myriadrf/LimeSDR-XTRX/hardware/rev5/Project Outputs/Pics/8L single outer 50.png

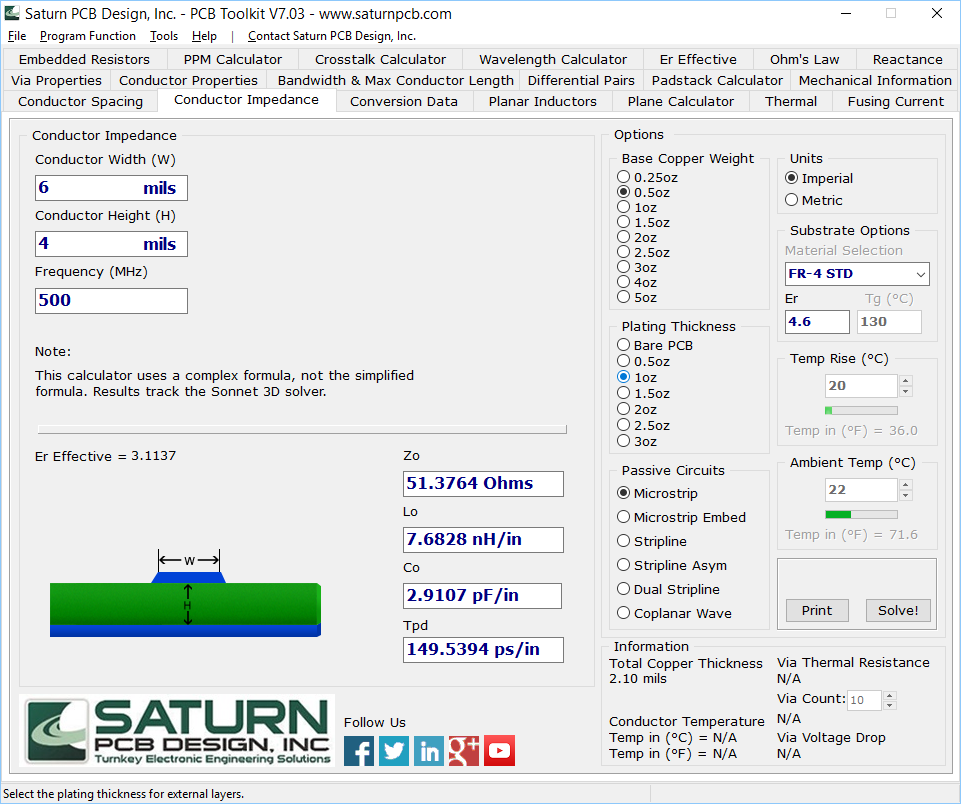
hardware/rev5/Project Outputs/Pics/8L single outer 50.png
