myriadrf/LimeSDR-XTRX/hardware/rev5/Project Outputs/Pics/8L stack.png

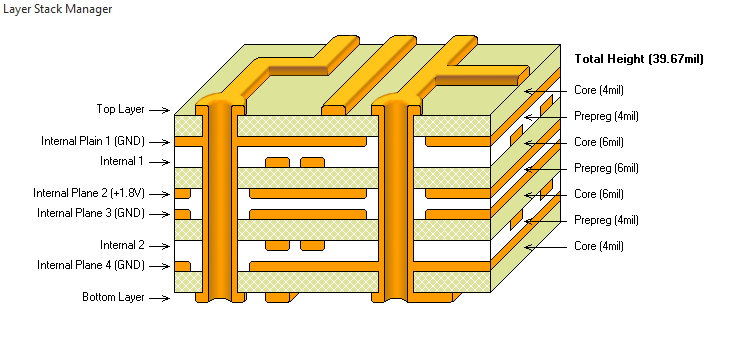
hardware/rev5/Project Outputs/Pics/8L stack.png
