myriadrf/LimeSDR-XTRX/hardware/rev5/Project Outputs/Pics/ARTIX-XC7A35T.jpg

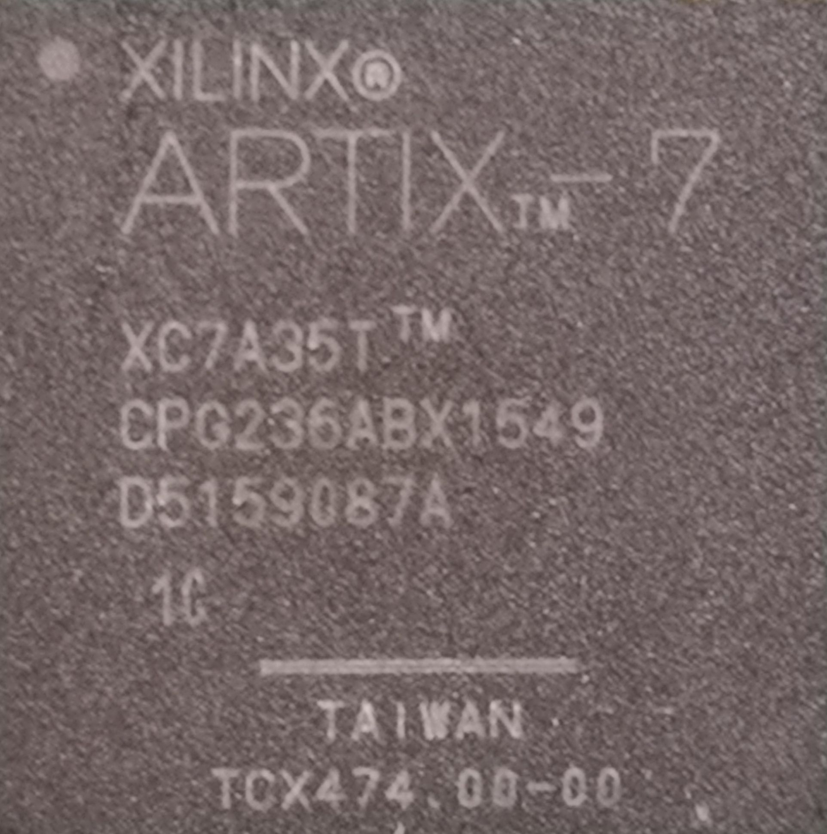
hardware/rev5/Project Outputs/Pics/ARTIX-XC7A35T.jpg
