myriadrf/LimeSDR-XTRX/hardware/rev5/Project Outputs/Pics/FPC Connector.png

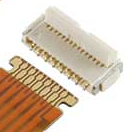
hardware/rev5/Project Outputs/Pics/FPC Connector.png
