myriadrf/LimeSDR-XTRX/hardware/rev5/Project Outputs/Pics/GPIO.jpg

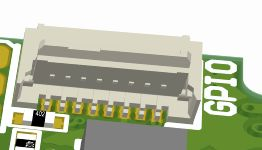
hardware/rev5/Project Outputs/Pics/GPIO.jpg
