myriadrf/LimeSDR-XTRX/hardware/rev5/Project Outputs/Pics/GPS Module.jpg

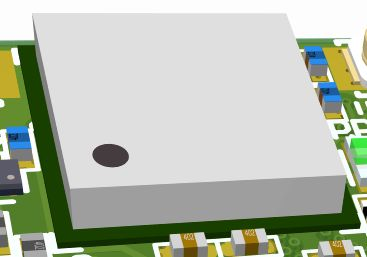
hardware/rev5/Project Outputs/Pics/GPS Module.jpg
