myriadrf/LimeSDR-XTRX/hardware/rev5/Project Outputs/Pics/JTAG.jpg

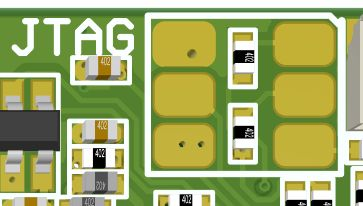
hardware/rev5/Project Outputs/Pics/JTAG.jpg
