myriadrf/LimeSDR-XTRX/hardware/rev5/Project Outputs/Pics/LMS7002M.jpg

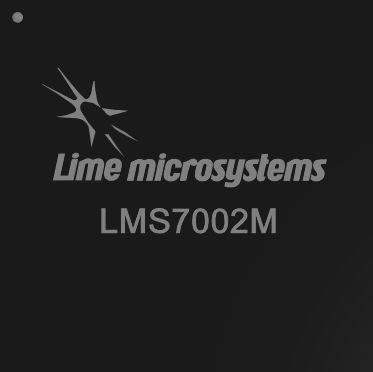
hardware/rev5/Project Outputs/Pics/LMS7002M.jpg
