myriadrf/LimeSDR-XTRX/hardware/rev5/Project Outputs/Pics/microUSB connector.jpg

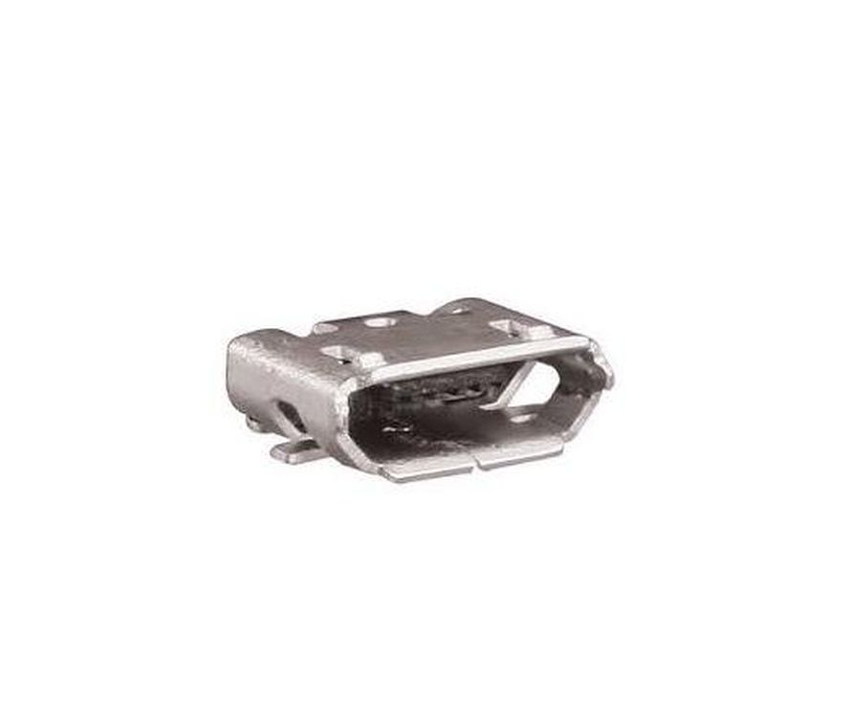
hardware/rev5/Project Outputs/Pics/microUSB connector.jpg
