myriadrf/LimeSDR-XTRX/hardware/rev5/Project Outputs/Pics/miniPCIe edge connector.jpg

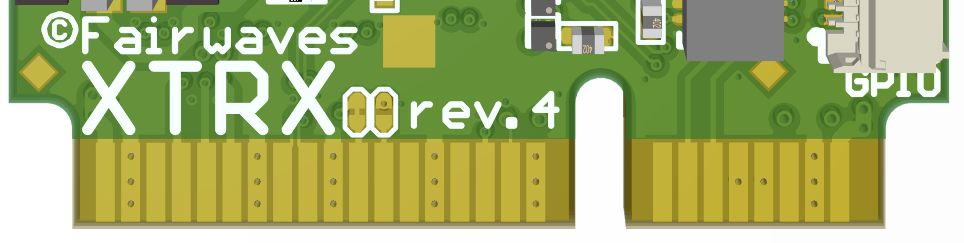
hardware/rev5/Project Outputs/Pics/miniPCIe edge connector.jpg
