myriadrf/LimeSDR-XTRX/hardware/rev5/Project Outputs/Pics/Rx IQ Input.jpg

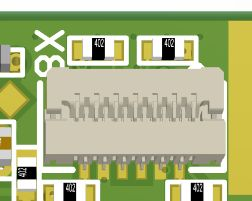
hardware/rev5/Project Outputs/Pics/Rx IQ Input.jpg
