myriadrf/LimeSDR-XTRX/hardware/rev5/Project Outputs/Pics/Transparently.png

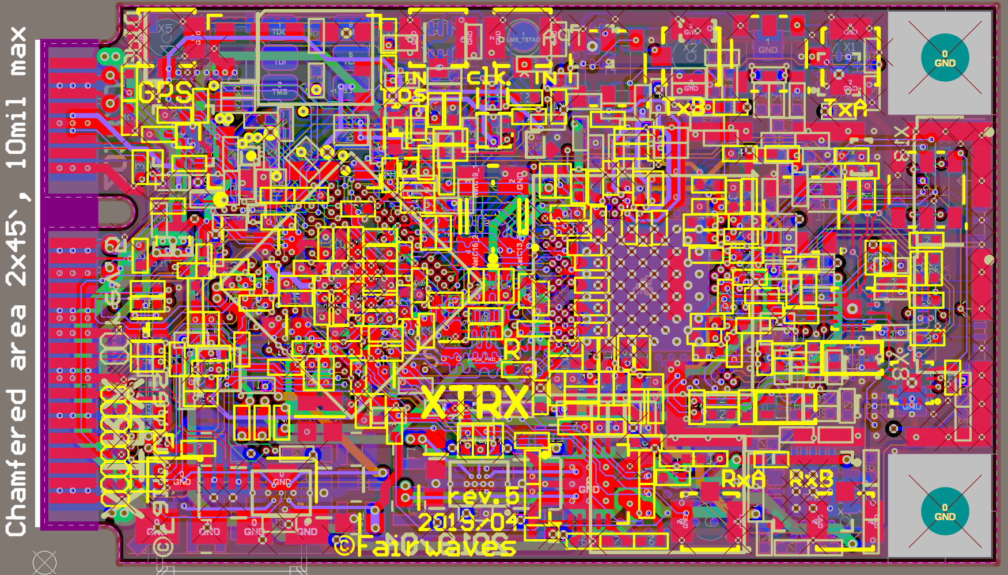
hardware/rev5/Project Outputs/Pics/Transparently.png
