myriadrf/LimeSDR-XTRX/hardware/rev5/Project Outputs/Pics/XTRXr5 pcb stack example.png

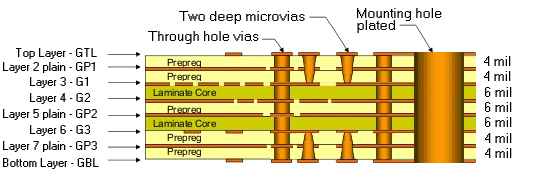
hardware/rev5/Project Outputs/Pics/XTRXr5 pcb stack example.png
