myriadrf/LimeSDR-XTRX/hardware/rev5/Project Outputs/XTRXr5 Func Diagram.PDF

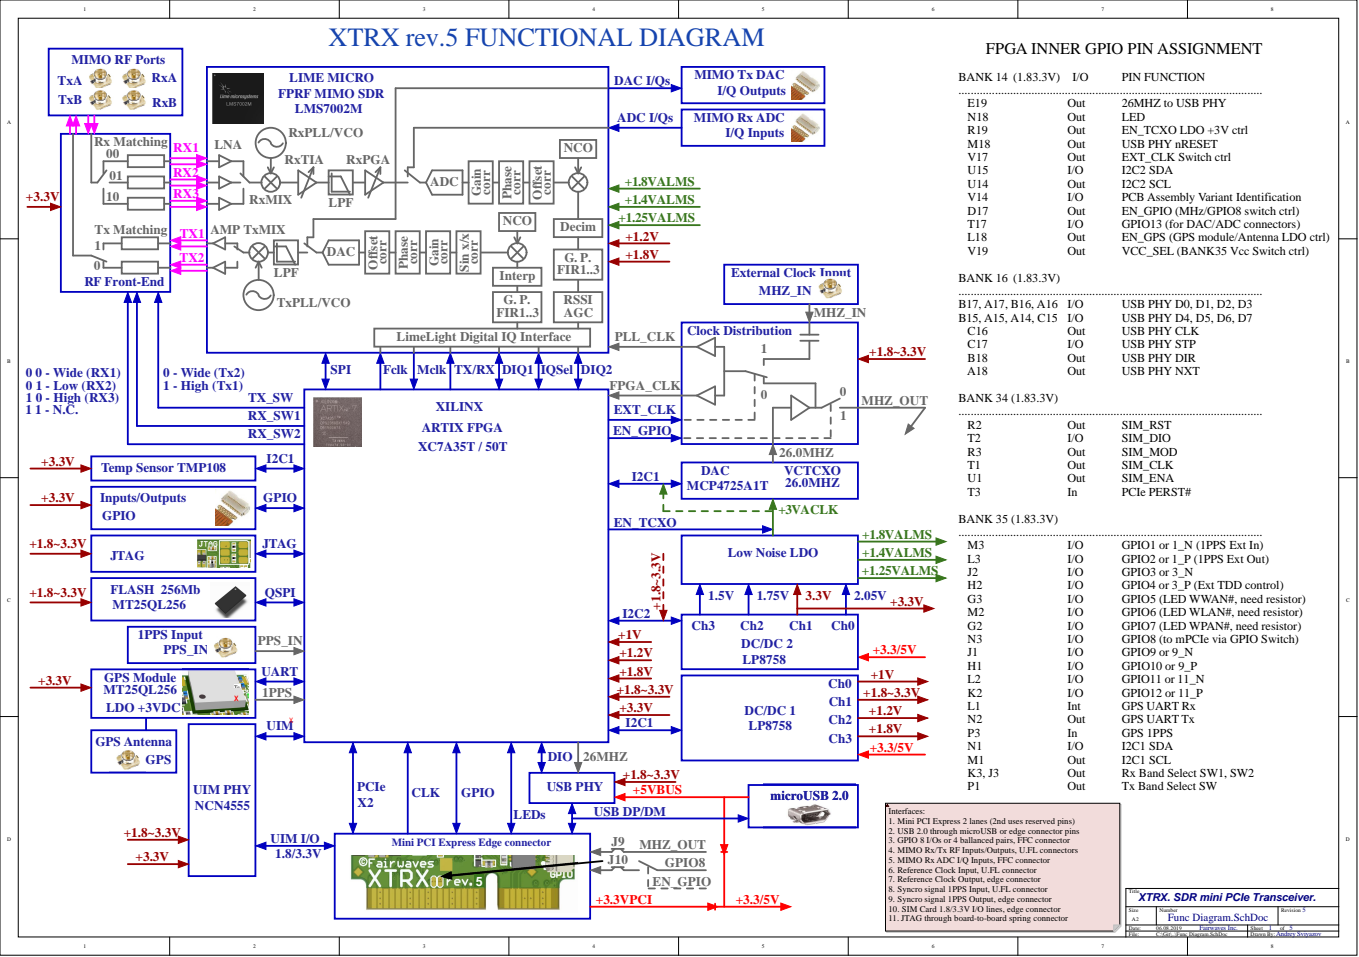
[picture p20: page 1]

XTRX rev.5 FUNCTIONAL DIAGRAM

FPGA INNER GPIO PIN ASSIGNMENT

LimeLight Digital IQ Interface

Interfaces:
1. Mini PCI Express 2 lanes (2nd uses reserved pins)
2. USB 2.0 through microUSB or edge connector pins
3. GPIO 8 I/Os or 4 ballanced pairs, FFC connector
4. MIMO Rx/Tx RF Inputs/Outputs, U.FL connectors
5. MIMO Rx ADC I/Q Inputs, FFC connector
6. Reference Clock Input, U.FL connector
7. Reference Clock Output, edge connector
8. Syncro signal 1PPS Input, U.FL connector
9. Syncro signal 1PPS Output, edge connector
10. SIM Card 1.8/3.3V I/O lines, edge connector
11. JTAG through board-to-board spring connector

Mini PCI Express Edge connector

Title
XTRX. SDR mini PCIe Transceiver.
