myriadrf/LimeSDR-XTRX/hardware/rev5/Project Outputs/XTRXr5_SCH_(Var 3.3V_I).pdf

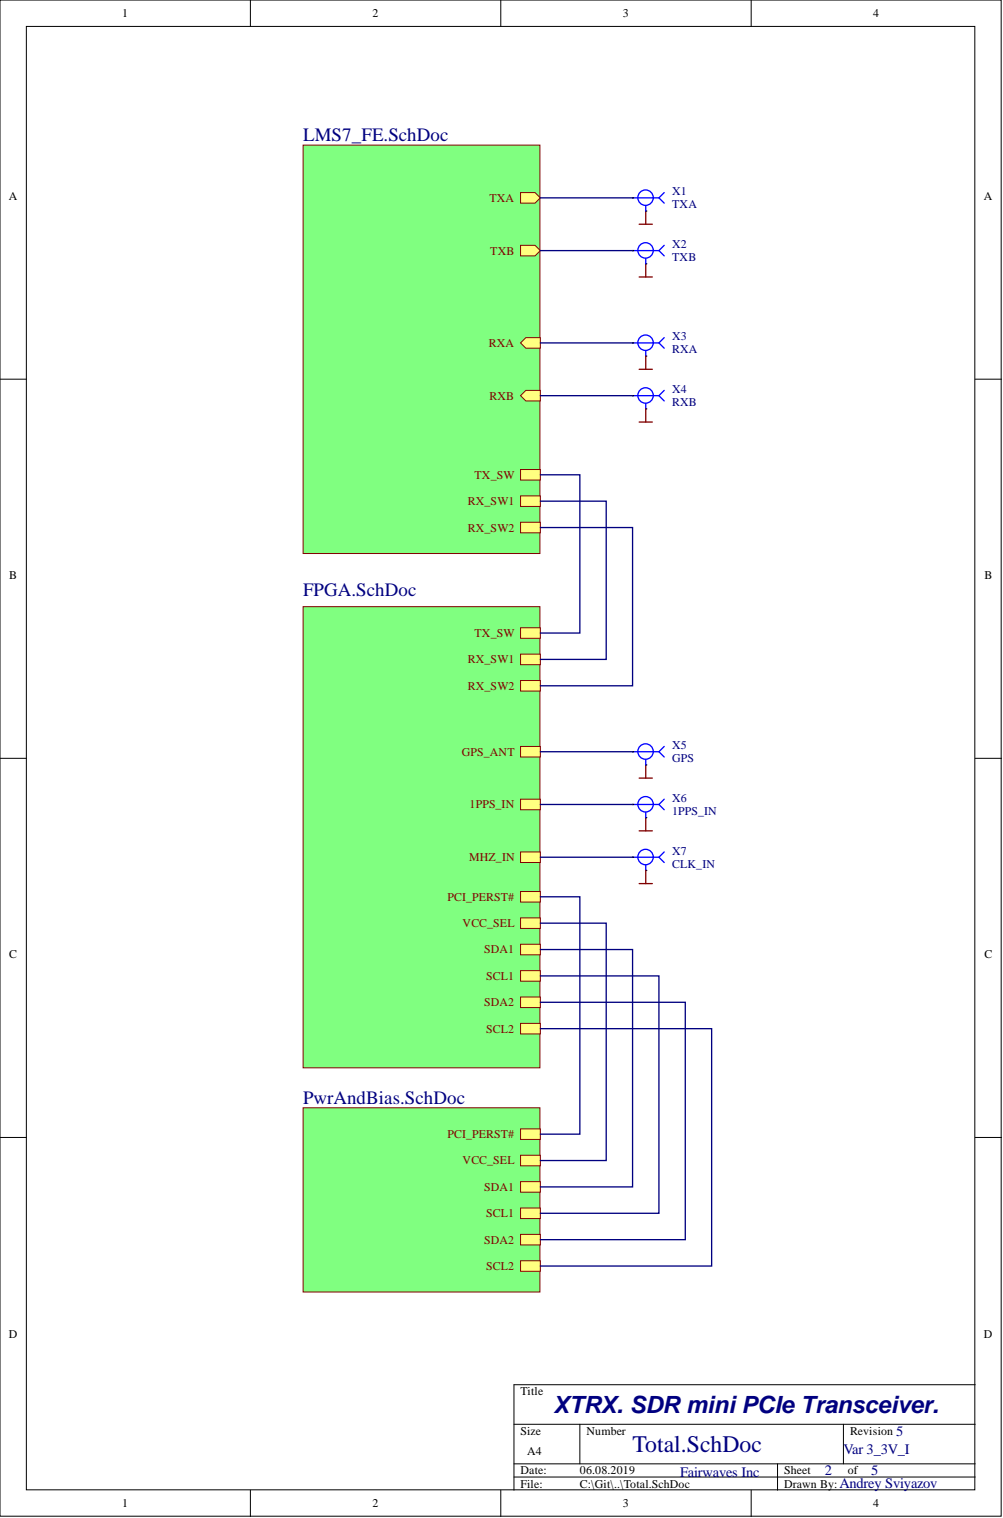
[picture p21: page 1]

Title
XTRX. SDR mini PCIe Transceiver.

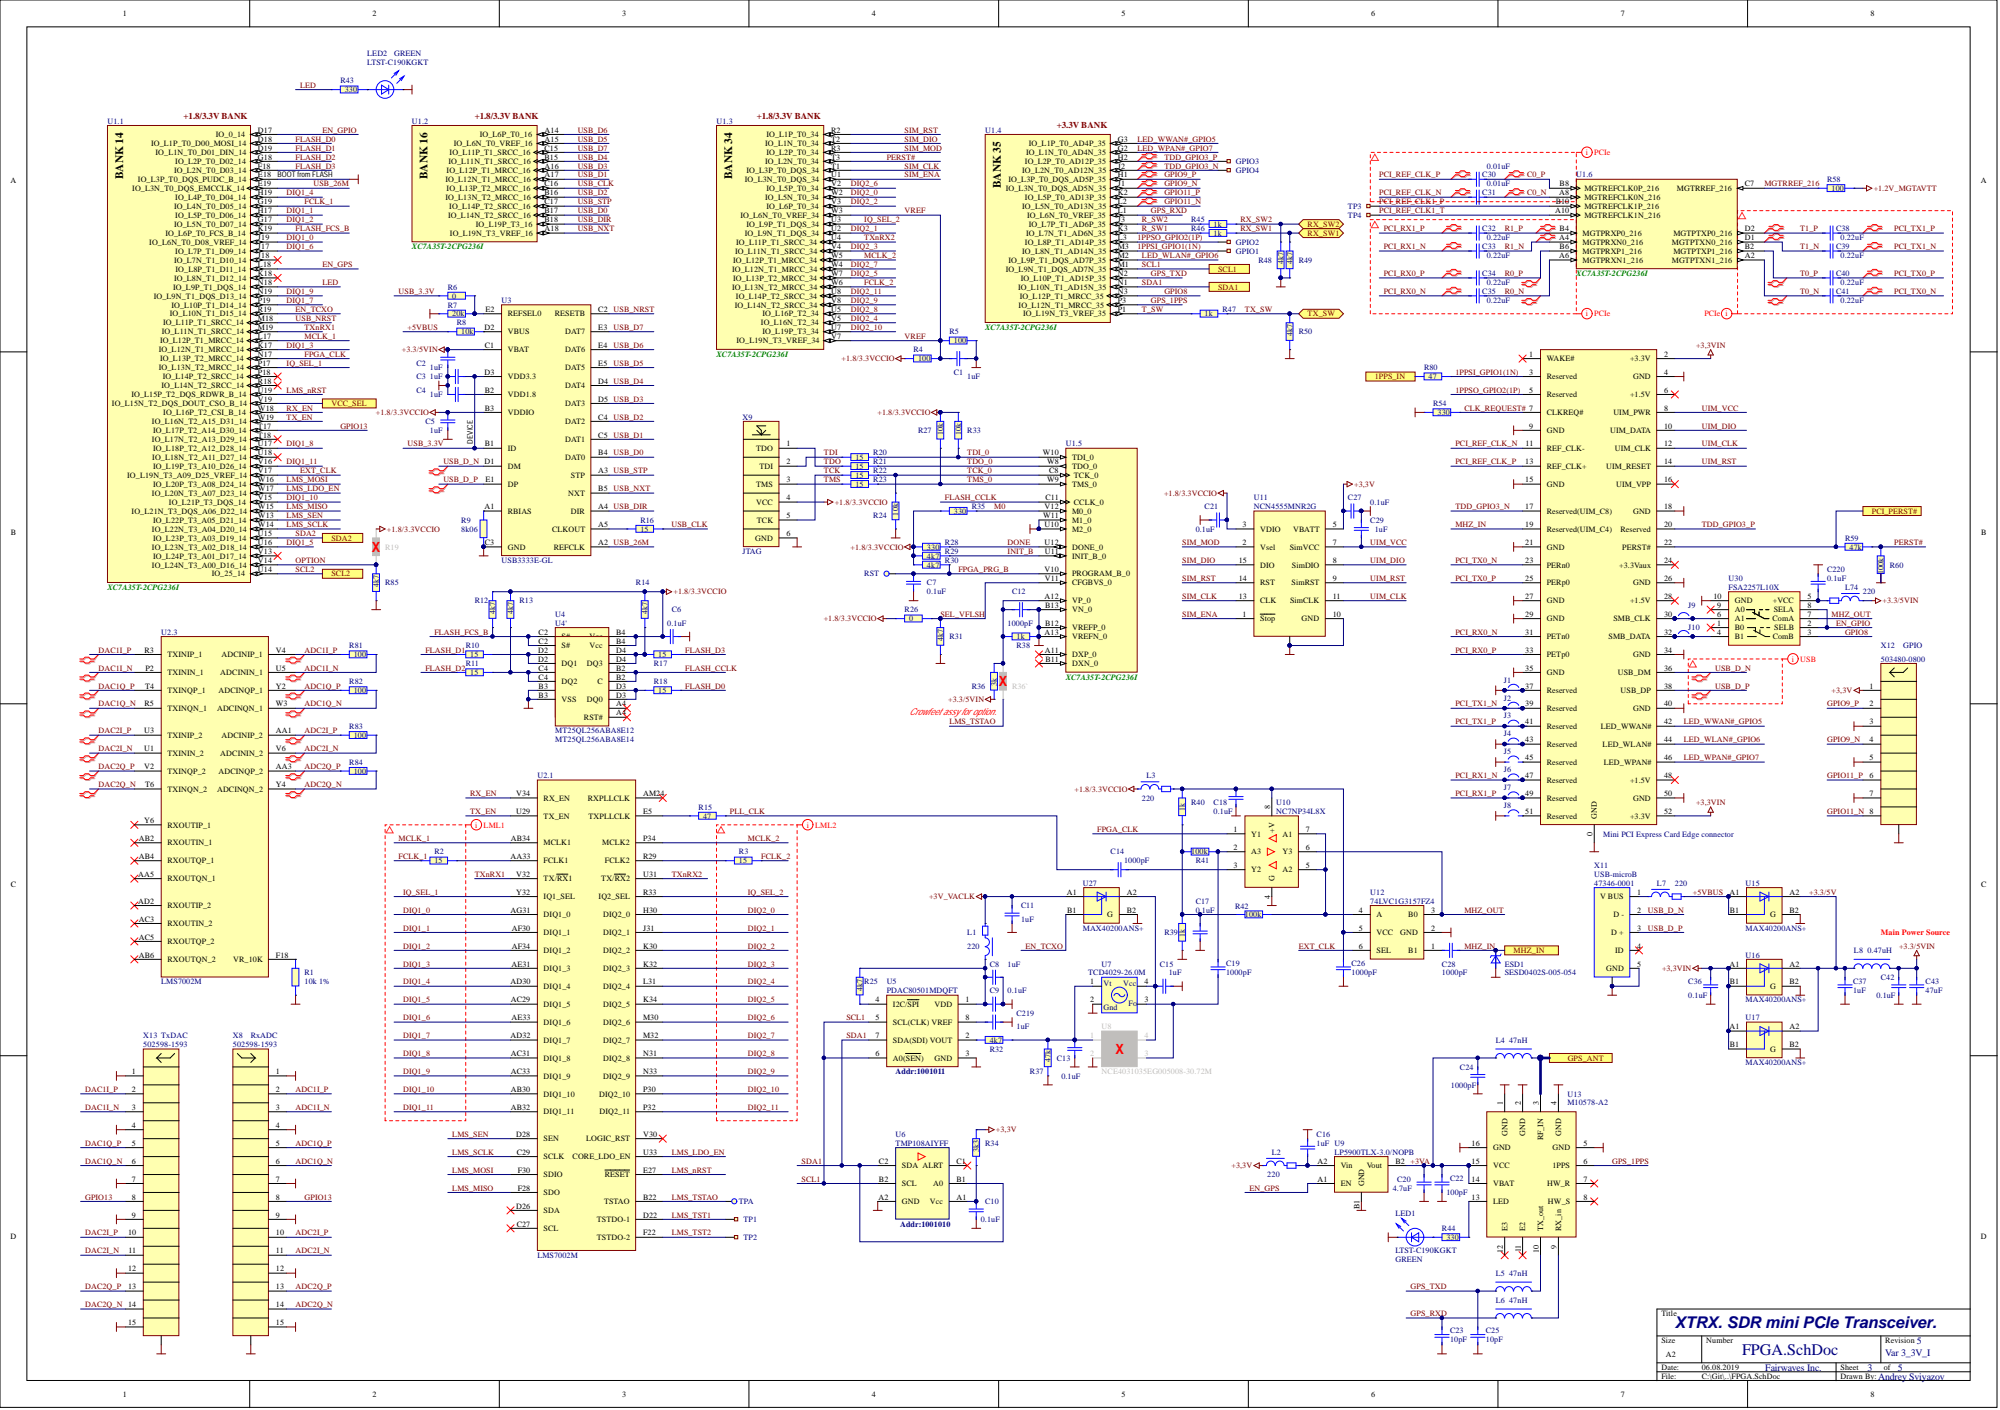
[picture p22: page 2]

Crowfeet assy for option.

ADC2Q_N | 100

Mini PCI Express Card Edge connector

SDA1 | SDA(SDI) 7

A0(SEN) 6

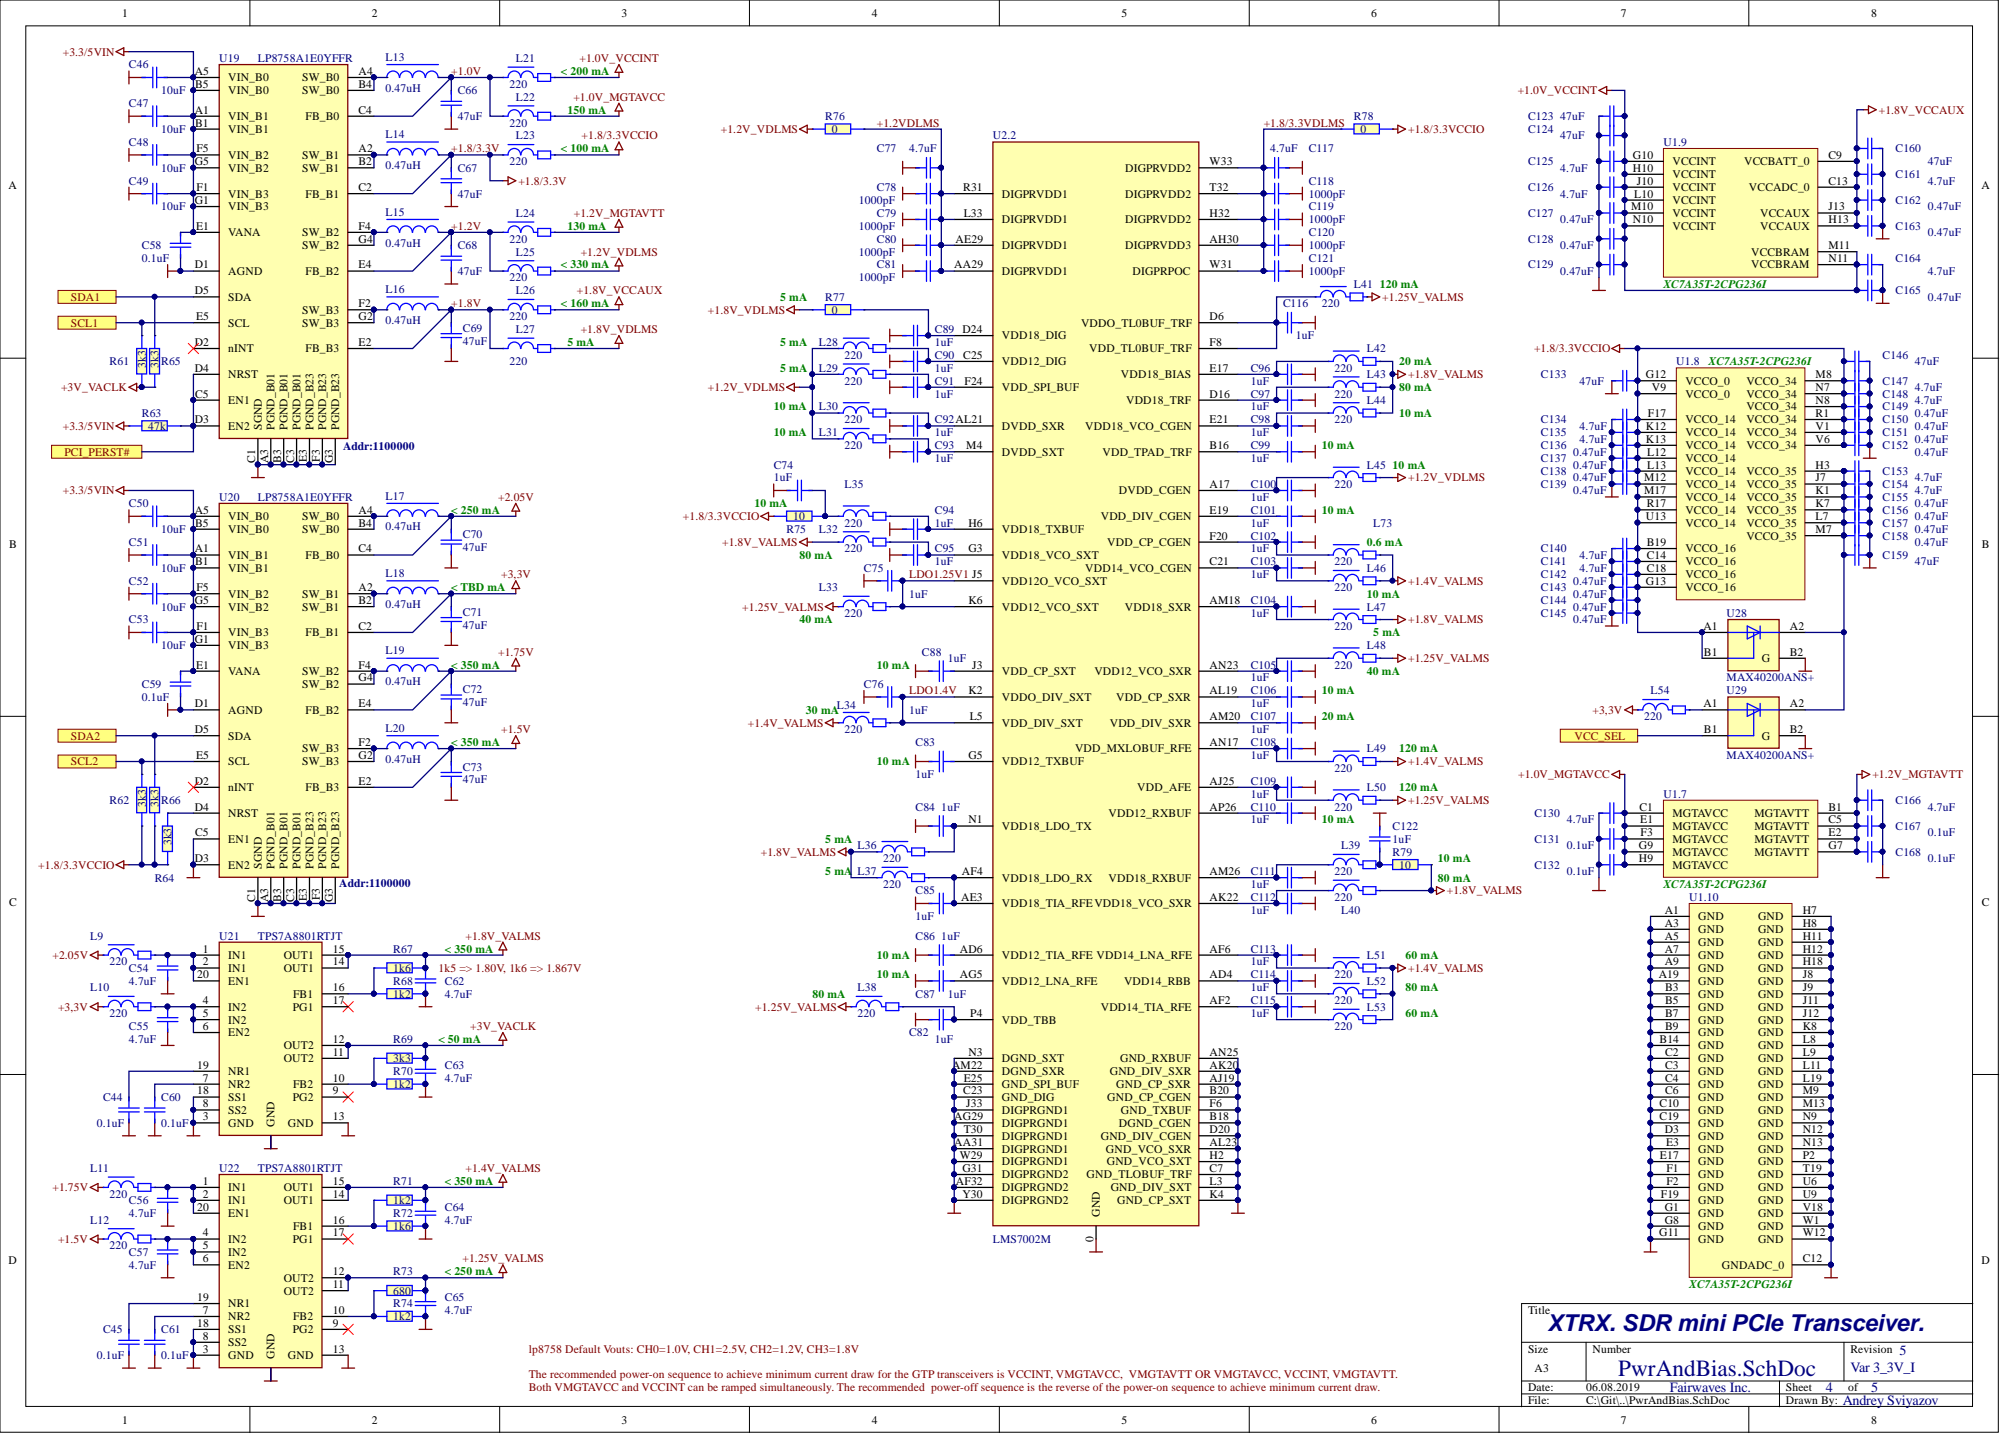
[picture p23: page 3]

J 7
K 1

A 3 | H 8
A 5 | H 1 1

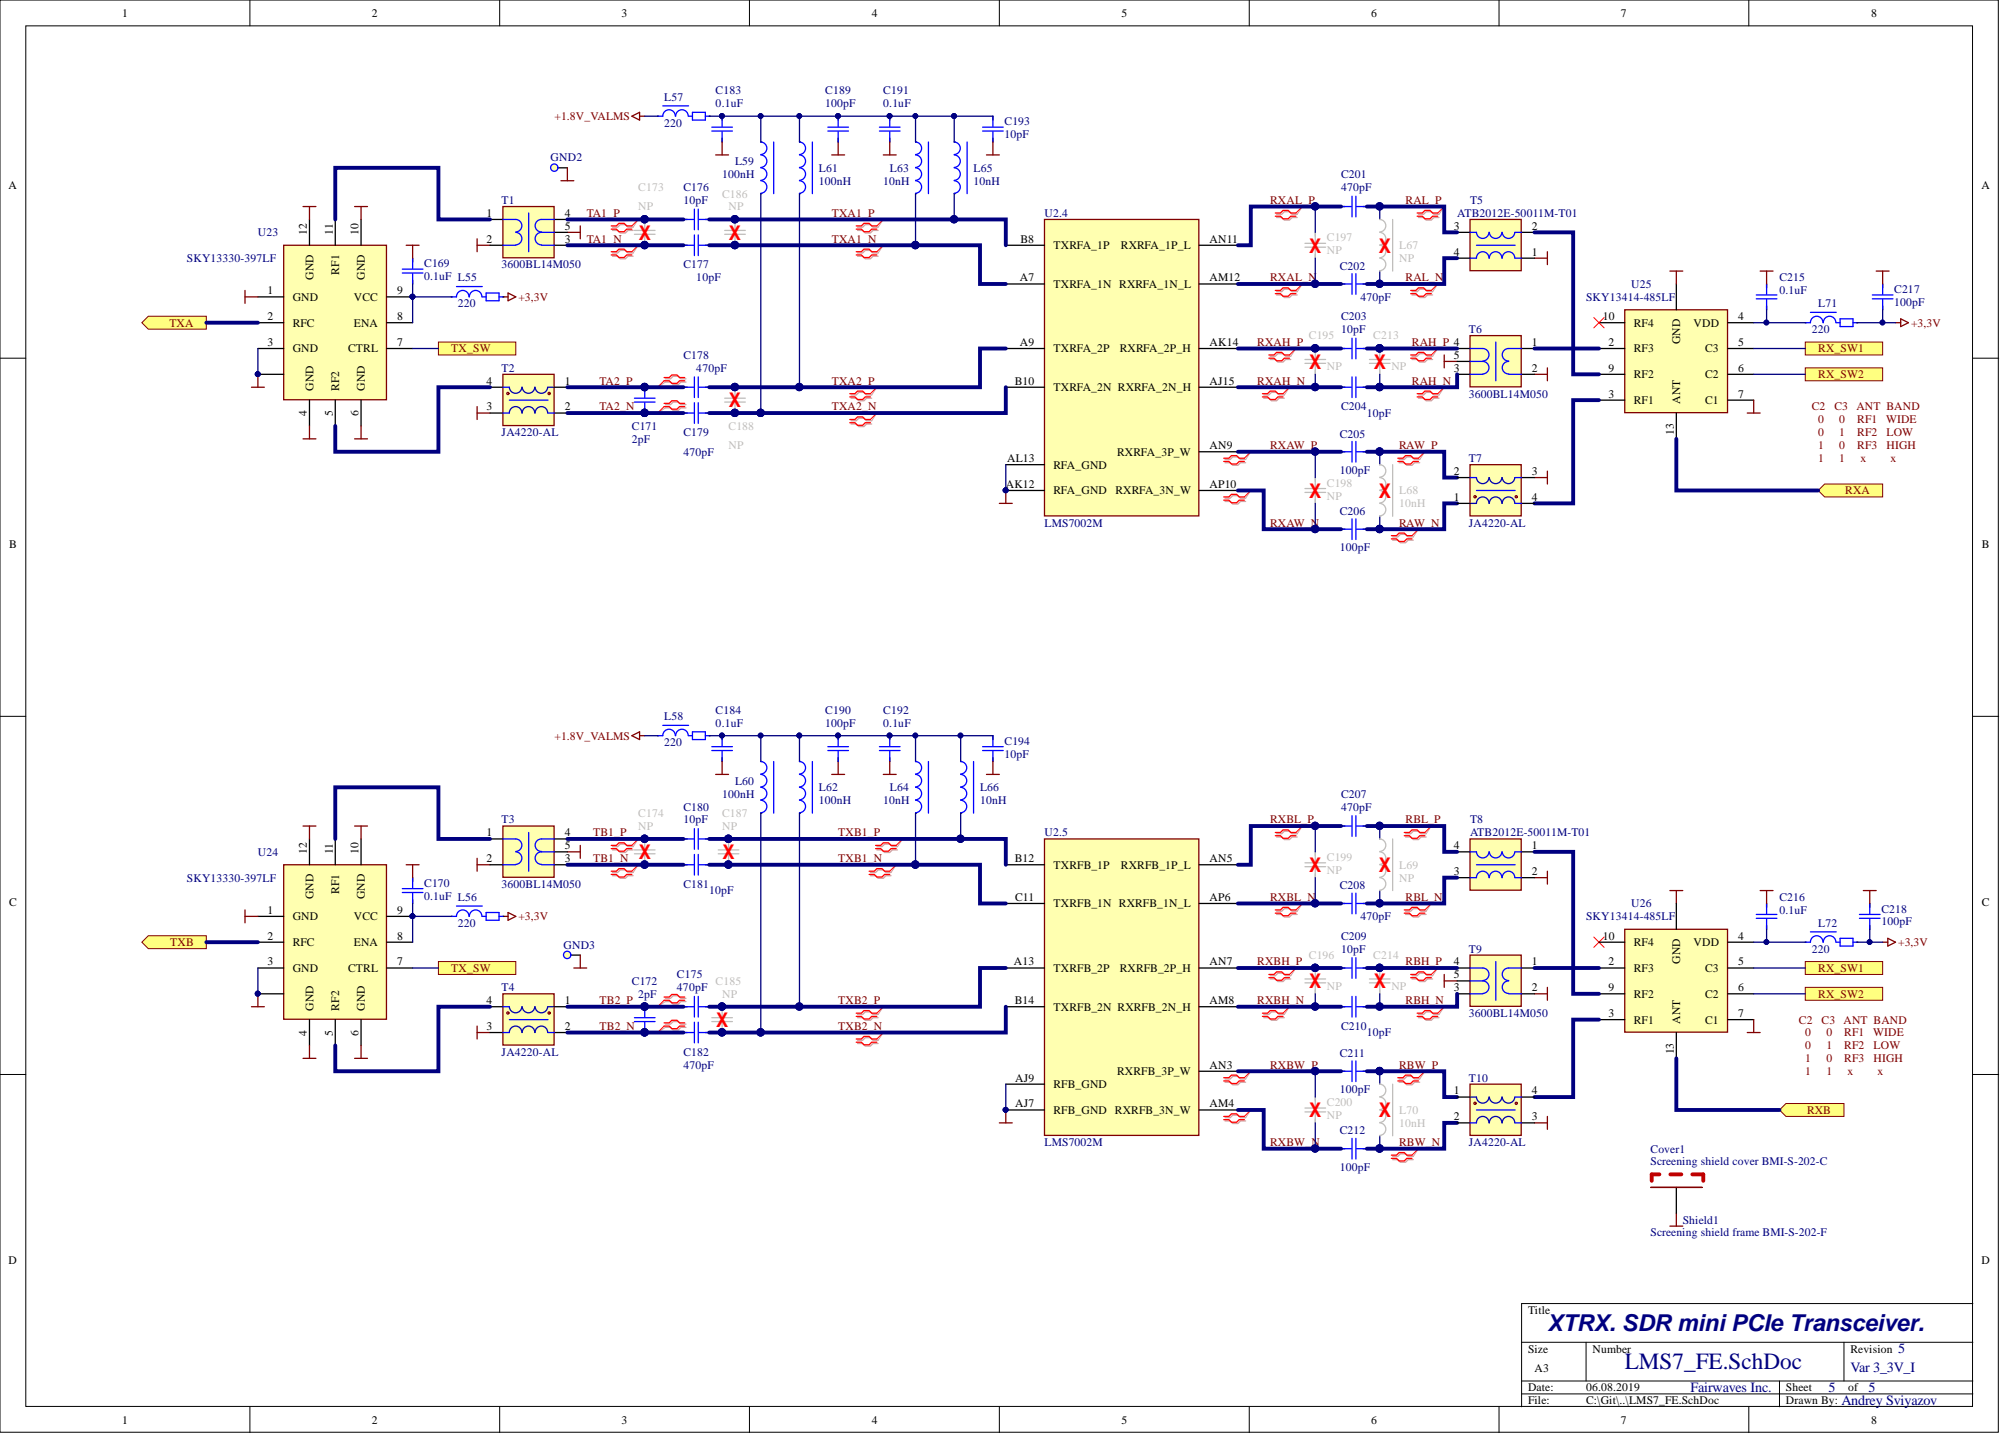
[picture p24: page 4]

RXAW_N

RAW_N

Cover1
Screening shield cover BMI-S-202-C

Shield1
Screening shield frame BMI-S-202-F
