myriadrf/LimeSDR-XTRX/hardware/rev5/Project Outputs/XTRXr5_assembly_(Var 3.3V).PDF

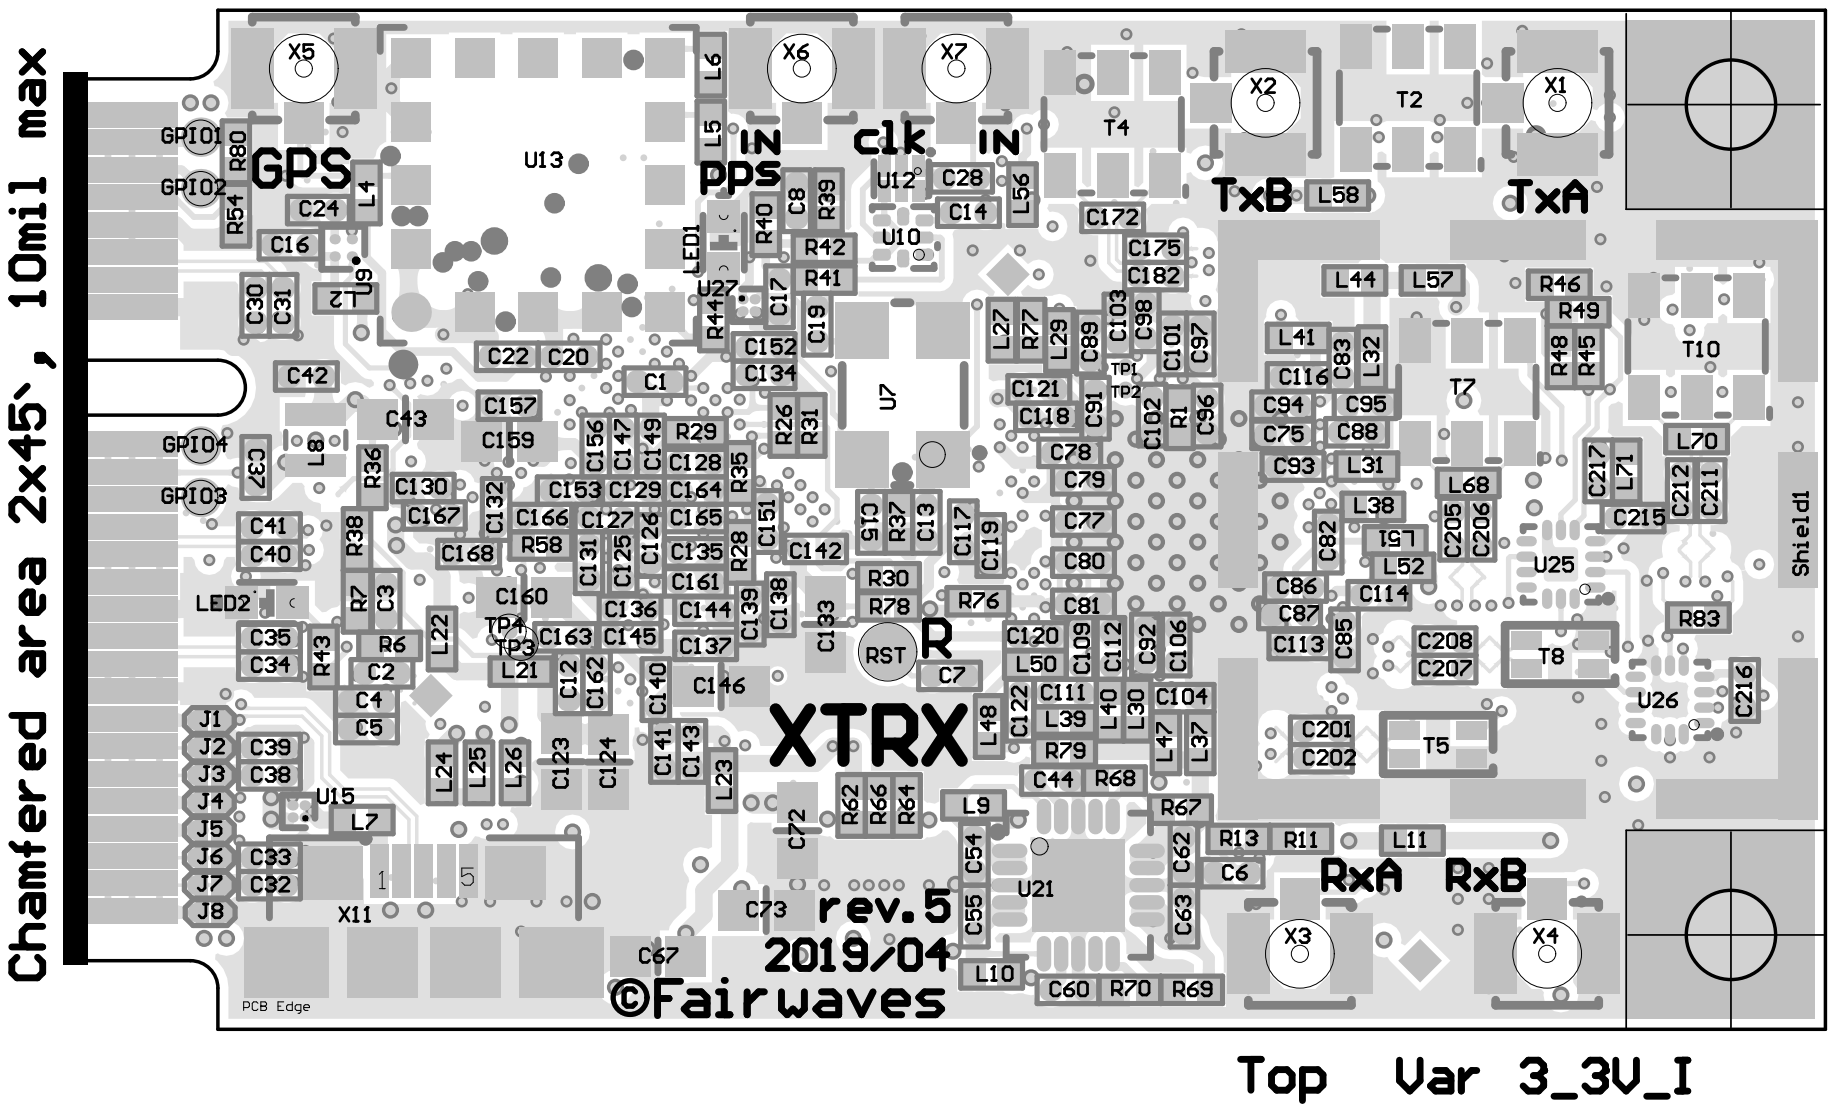
[picture p43: page 1]

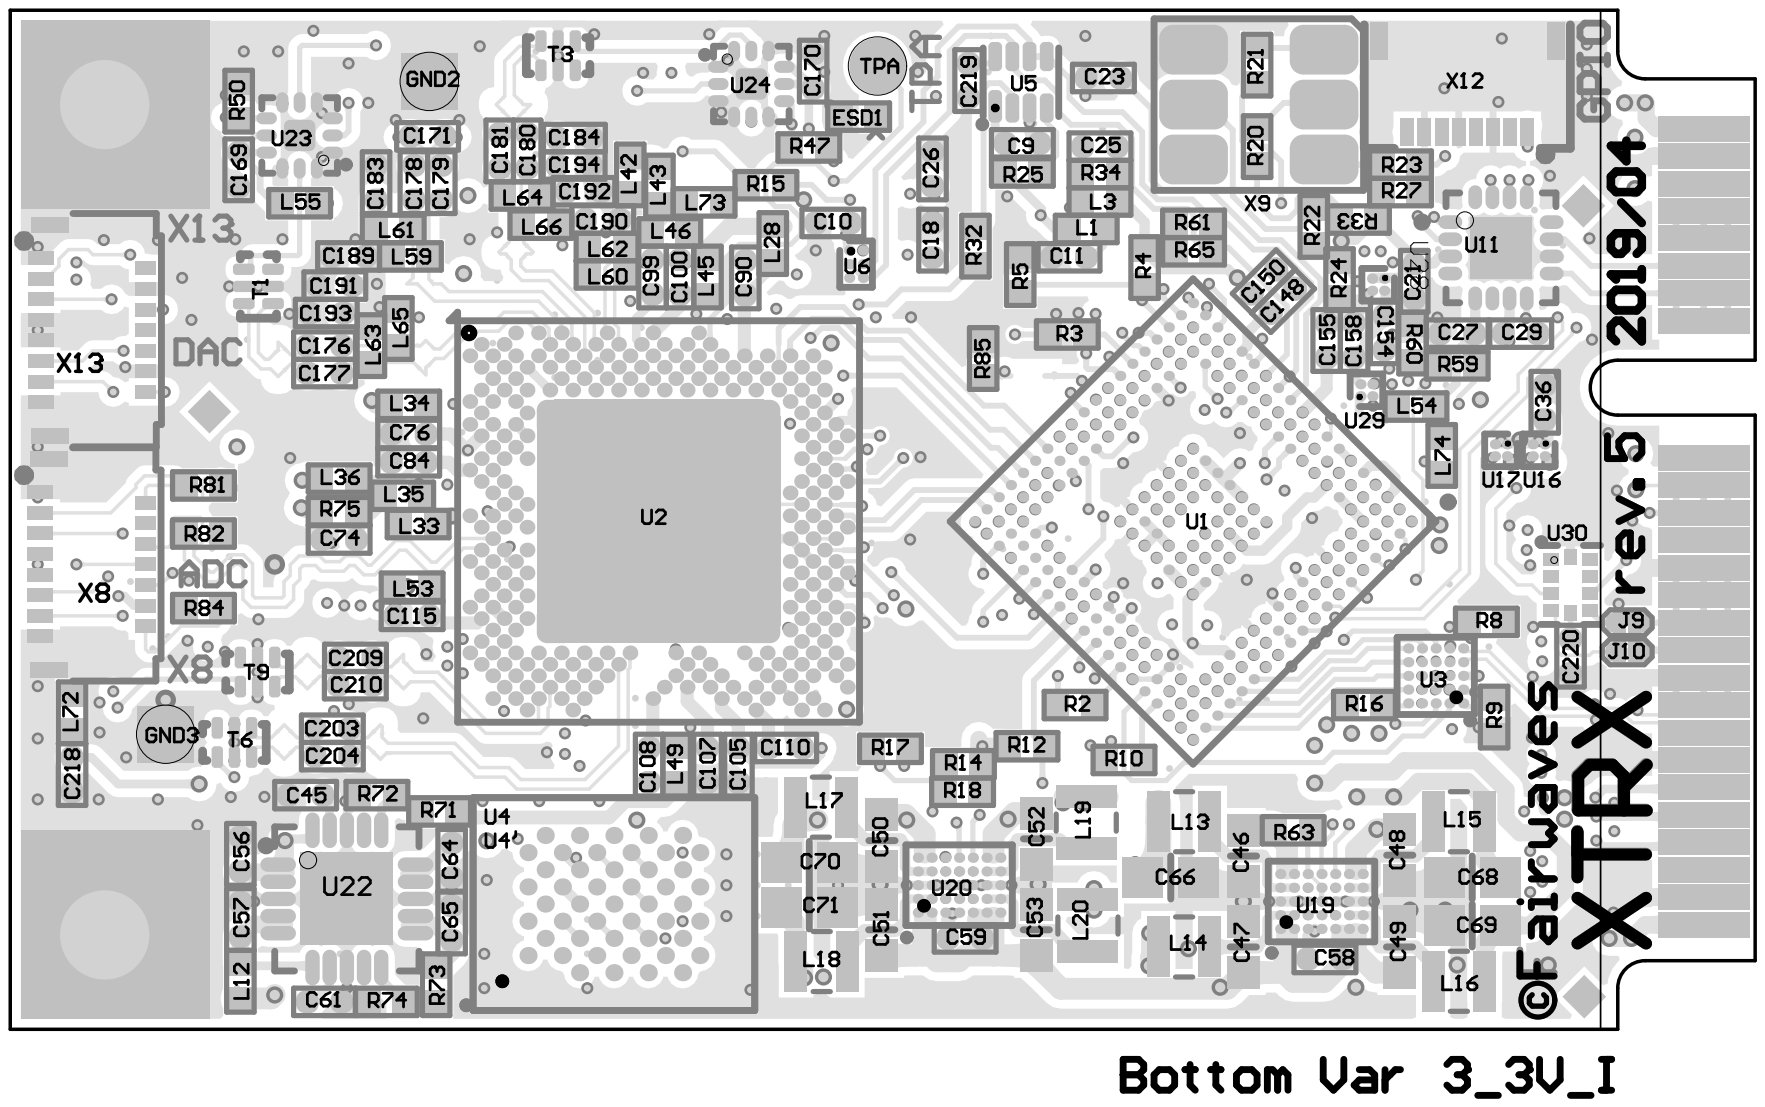
[picture p44: page 2]
